MordFIdel/SOCORAD32/3D_Files/dimension.JPG

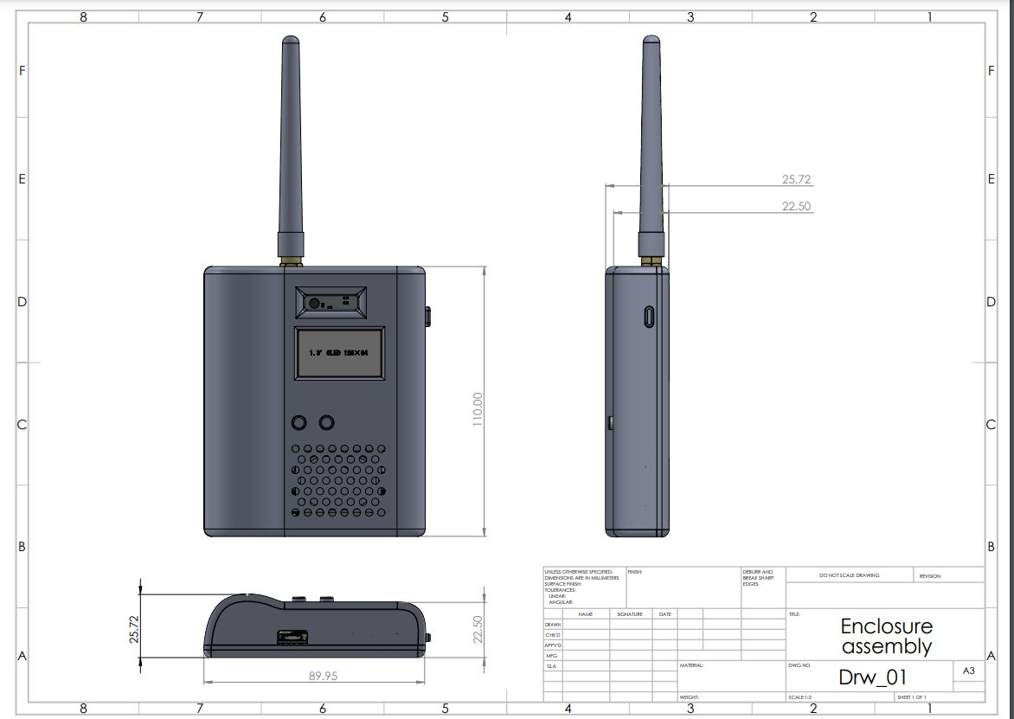
3D_Files/dimension.JPG
