MordFIdel/SOCORAD32/SCRD32_firmware_official/main/ui.c

#include "main.h"

#define TAG "UI"

SSD1306_t dev;
uint8_t gChannelNum =	0;
uint8_t gVolume  	=	0;
uint8_t gVox     	=	0;
float   gRFV	 	=	0;
float   gTFV	  	=	0;
bool    gPowerLevel = 	LOW_LEVEL; //0:High, 1:Low
bool 	gBand   	=	WIDE_BAND; 
bool    gBusyLock	=   false;

bool	gScreenRefresh = false;
uint8_t gRxCtcss	=	0;
uint8_t gTxCtcss	=	0;


channel_config_t channelInfo[MAX_CHANNEL_NUM] = {
	//RFV		TFV		  RxCT,TxCT,Vox, BAND,		 PowerLevel
	{410.025,	410.025,	1,	1,	3,	WIDE_BAND,	HIGH_LEVEL},
	{410.850,	410.850,	2,	2,	3,	WIDE_BAND,	HIGH_LEVEL},
	{411.675,	411.675,	3,	3,	3,	WIDE_BAND,	HIGH_LEVEL},
	{412.500,	412.500,	4,	4,	3,	WIDE_BAND,	HIGH_LEVEL},
	{413.325,	413.325,	5,	5,	3,	WIDE_BAND,	HIGH_LEVEL},
	{414.150,	414.150,	6,	6,	3,	WIDE_BAND,	HIGH_LEVEL},
	{414.975,	414.975,	7,	7,	3,	WIDE_BAND,	HIGH_LEVEL},
	{415.800,	415.800,	8,	8,	3,	WIDE_BAND,	HIGH_LEVEL},
	{416.625,	416.625,	9,	9,	3,	WIDE_BAND,	HIGH_LEVEL},
	{417.450,	417.450,	10,	10,	3,	WIDE_BAND,	HIGH_LEVEL},
	{418.275,	418.275,	11,	11,	3,	WIDE_BAND,	HIGH_LEVEL},
	{419.100,	419.100,	12,	12,	3,	WIDE_BAND,	HIGH_LEVEL},
	{419.925,	419.925,	13,	13,	3,	WIDE_BAND,	HIGH_LEVEL},
	{420.750,	420.750,	14,	14,	3,	WIDE_BAND,	HIGH_LEVEL},
	{421.575,	421.575,	15,	15,	3,	WIDE_BAND,	HIGH_LEVEL},
	{422.400,	422.400,	16,	16,	3,	WIDE_BAND,	HIGH_LEVEL},
	{423.225,	423.225,	17,	17,	3,	WIDE_BAND,	HIGH_LEVEL},
	{424.050,	424.050,	18,	18,	3,	WIDE_BAND,	HIGH_LEVEL},
	{424.875,	424.875,	19,	19,	3,	WIDE_BAND,	HIGH_LEVEL},
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
	0x00, 0x00, 0x00, 0x00, 0x00, 0x00, 0x00, 0x00, 0x00, 0x00, 0x00, 0x00, 0x00, 0x00, 0x00, 0x00, 
	0x00, 0x00, 0x00, 0x00, 0x00, 0x00, 0x00, 0x00, 0x00, 0x00, 0x00, 0x00, 0x00, 0x00, 0x00, 0x00, 
	0x00, 0x00, 0x00, 0x00, 0x00, 0x00, 0x00, 0x00, 0x00, 0x00, 0x00, 0x00, 0x00, 0x00, 0x00, 0x00, 
	0x00, 0x00, 0x00, 0x00, 0x00, 0x00, 0x00, 0x06, 0x00, 0x00, 0x00, 0x00, 0x00, 0x00, 0x00, 0x00, 
	0x00, 0x00, 0x00, 0x03, 0x00, 0x00, 0x00, 0x06, 0x60, 0x00, 0x00, 0x00, 0x00, 0x00, 0x00, 0x00, 
	0x00, 0x00, 0x00, 0x03, 0x00, 0x00, 0x00, 0x06, 0x60, 0x00, 0x00, 0x00, 0x00, 0x00, 0x00, 0x00, 
	0x00, 0x00, 0x00, 0x03, 0x00, 0x00, 0x00, 0x06, 0x00, 0x00, 0x00, 0x00, 0x00, 0x00, 0x00, 0x00, 
	0x00, 0x00, 0x00, 0x03, 0x00, 0xf0, 0xf0, 0x76, 0x63, 0x60, 0xec, 0x00, 0x00, 0x00, 0x00, 0x00, 
	0x00, 0x00, 0x00, 0x03, 0x01, 0xf8, 0xf8, 0xfe, 0x63, 0xf1, 0xfc, 0x00, 0x00, 0x00, 0x00, 0x00, 
	0x00, 0x00, 0x00, 0x03, 0x03, 0x1c, 0x0d, 0xc6, 0x63, 0x1b, 0x8c, 0x00, 0x00, 0x00, 0x00, 0x00, 
	0x00, 0x00, 0x00, 0x03, 0x03, 0x0c, 0x0d, 0x86, 0x63, 0x1b, 0x0c, 0x00, 0x00, 0x00, 0x00, 0x00, 
	0x00, 0x00, 0x00, 0x03, 0x03, 0x0c, 0xfd, 0x86, 0x63, 0x1b, 0x0c, 0x00, 0x00, 0x00, 0x00, 0x00, 
	0x00, 0x00, 0x00, 0x03, 0x03, 0x0d, 0x8d, 0x86, 0x63, 0x1b, 0x0c, 0x00, 0x00, 0x00, 0x00, 0x00, 
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
};

unsigned char Progress [] = {
	// 'Progress, 24x4px
	0xff, 0xff, 0xff, 
	0xff, 0xff, 0xff, 
	0xff, 0xff, 0xff, 
	0xff, 0xff, 0xff
};

static void uiInit(void)
{
    #if CONFIG_I2C_INTERFACE
	ESP_LOGI(TAG, "INTERFACE is i2c");
	ESP_LOGI(TAG, "CONFIG_SDA_GPIO=%d",CONFIG_SDA_GPIO);
	ESP_LOGI(TAG, "CONFIG_SCL_GPIO=%d",CONFIG_SCL_GPIO);
	ESP_LOGI(TAG, "CONFIG_RESET_GPIO=%d",CONFIG_RESET_GPIO);
	i2c_master_init(&dev, CONFIG_SDA_GPIO, CONFIG_SCL_GPIO, CONFIG_RESET_GPIO);
#endif // CONFIG_I2C_INTERFACE

#if CONFIG_SPI_INTERFACE
	ESP_LOGI(TAG, "INTERFACE is SPI");
	ESP_LOGI(TAG, "CONFIG_MOSI_GPIO=%d",CONFIG_MOSI_GPIO);
	ESP_LOGI(TAG, "CONFIG_SCLK_GPIO=%d",CONFIG_SCLK_GPIO);
	ESP_LOGI(TAG, "CONFIG_CS_GPIO=%d",CONFIG_CS_GPIO);
	ESP_LOGI(TAG, "CONFIG_DC_GPIO=%d",CONFIG_DC_GPIO);
	ESP_LOGI(TAG, "CONFIG_RESET_GPIO=%d",CONFIG_RESET_GPIO);
	spi_master_init(&dev, CONFIG_MOSI_GPIO, CONFIG_SCLK_GPIO, CONFIG_CS_GPIO, CONFIG_DC_GPIO, CONFIG_RESET_GPIO);
#endif // CONFIG_SPI_INTERFACE

#if CONFIG_FLIP
	dev._flip = true;
	ESP_LOGW(TAG, "Flip upside down");
#endif

#if CONFIG_SSD1306_128x64
	ESP_LOGI(TAG, "Panel is 128x64");
	ssd1306_init(&dev, 128, 64);
#endif // CONFIG_SSD1306_128x64
#if CONFIG_SSD1306_128x32
	ESP_LOGI(TAG, "Panel is 128x32");
	ssd1306_init(&dev, 128, 32);
#endif // CONFIG_SSD1306_128x32

	ssd1306_contrast(&dev, 0xff);
}

static float getToneFreq(uint8_t ctcss_code)
{
	if (ctcss_code >= 0 && ctcss_code <= 39)
		return tone_freq[ctcss_code];
	else
		return 0; //I suggest this return to be other than 0 for later debug.
}

void getChannelInfo(uint8_t channel)
{
	if(channel < MAX_CHANNEL_NUM)
	{
		gRFV = channelInfo[gChannelNum].rfv;
		gTFV = channelInfo[gChannelNum].tfv;
		//gToneFreq = getToneFreq(channelInfo.rx_ctcss);
		gRxCtcss = channelInfo[gChannelNum].rx_ctcss;
		gTxCtcss = channelInfo[gChannelNum].tx_ctcss;

		gBand = channelInfo[gChannelNum].band;
		gVox  = channelInfo[gChannelNum].vox;
		gPowerLevel = channelInfo[gChannelNum].power_level;
	}
}
void uiBootScreenLoad(uint16_t delayms)
{
	// gChannelNum = 3;
	// saveChannelInfo();

	readChannelInfo();//read from eeprom
		
	gVolume = 5;

	getChannelInfo(gChannelNum);	

    uint16_t delay = delayms/3;
    ssd1306_clear_screen(&dev, false);
	ssd1306_bitmaps(&dev, 0, 0, Bootup, 128, 64, false);
	ssd1306_bitmaps(&dev, 23, 51, Progress, 24, 4, false);
	vTaskDelay(delay / portTICK_PERIOD_MS);
	ssd1306_bitmaps(&dev, 40, 51, Progress, 24, 4, false);
	vTaskDelay(delay / portTICK_PERIOD_MS);
	ssd1306_bitmaps(&dev, 61, 51, Progress, 24, 4, false);
	vTaskDelay(delay / portTICK_PERIOD_MS);
	ssd1306_bitmaps(&dev, 81, 51, Progress, 24, 4, false);
}

void uiMainScreenLoad(void)
{
    ssd1306_clear_screen(&dev, false);
	// ssd1306_display_text(&dev, 0, "CH:CH35,Vol:8 ", 14, false);
	// ssd1306_bitmaps(&dev, 110, 0, Volume_4, 16, 8, false);
	// ssd1306_display_text(&dev, 2, "Tx:450.025M, P:H", 16, false);
	// ssd1306_display_text(&dev, 5, "Rx:450.025M", 11, false);
	// ssd1306_display_text(&dev, 7, "Vox   BAND   Cts", 16, false);

    setChannelAndVolume();
    setTxFreqAndPower();
    setRxFreq();
    setVoxBandCts();
}

static void setVolumeImg(void)
{
    if(gVolume == 0)                         ssd1306_bitmaps(&dev, 112, 0, Volume_0, 16, 8, false);
    else if(gVolume == 1 || gVolume == 2)    ssd1306_bitmaps(&dev, 112, 0, Volume_1, 16, 8, false);
    else if(gVolume >= 3 && gVolume <= 5)    ssd1306_bitmaps(&dev, 112, 0, Volume_2, 16, 8, false);
    else if(gVolume >= 6 && gVolume <= 8)    ssd1306_bitmaps(&dev, 112, 0, Volume_3, 16, 8, false);
}

void setChannelAndVolume()
{
    char buf[20];
    memset(buf, 0, sizeof(buf));
    sprintf(buf, "CH:CH%02d, Vol:%01d", gChannelNum, gVolume);
    ssd1306_clear_line(&dev, 0, 0);
    ssd1306_display_text(&dev, 0, buf, 14, false);
    setVolumeImg();
}

void setTxFreqAndPower()
{
    char buf[20];
    memset(buf, 0, sizeof(buf));
    if(gPowerLevel == HIGH_LEVEL)
        sprintf(buf, "Tx:%.3fM, P:H", gTFV);
    else if(gPowerLevel == LOW_LEVEL)
        sprintf(buf, "Tx:%.3fM, P:L", gTFV);
    
    ssd1306_clear_line(&dev, 2, 0);
    ssd1306_display_text(&dev, 2, buf, 16, false);
}

void setRxFreq()
{
    char buf[20];
    memset(buf, 0, sizeof(buf));
    sprintf(buf, "Rx:%.3fM", gRFV);
    
    ssd1306_clear_line(&dev, 5, 0);
    ssd1306_display_text(&dev, 5, buf, 16, false);
}

void setVoxBandCts()
{
    char buf[22];
    memset(buf, 0, sizeof(buf));
	if(gBand == WIDE_BAND)
    	sprintf(buf, "Vox:%d B:W, %d %d", gVox, gRxCtcss, gTxCtcss);
	else if(gBand == NARROW_BAND)
		sprintf(buf, "Vox:%d B:N, %d %d", gVox, gRxCtcss, gTxCtcss);
    
	// ssd1306_clear_line(&dev, 6, 0);
	// ssd1306_display_text(&dev, 6, "         Cts(Hz)", 16, false);
	ssd1306_clear_line(&dev, 7, 0);
    ssd1306_display_text(&dev, 7, buf, 16, false);
}

void uiTask(void *arg)
{
    uiInit();
    uiBootScreenLoad(1500);
	uiMainScreenLoad();
    while(1)
    {
		if(gScreenRefresh)
		{
			uiMainScreenLoad();
			gScreenRefresh = false;
		}
        vTaskDelay(pdMS_TO_TICKS(10));
    }
}
